JX5S/DP_aux_emulator/JLCPCB settings/1.png

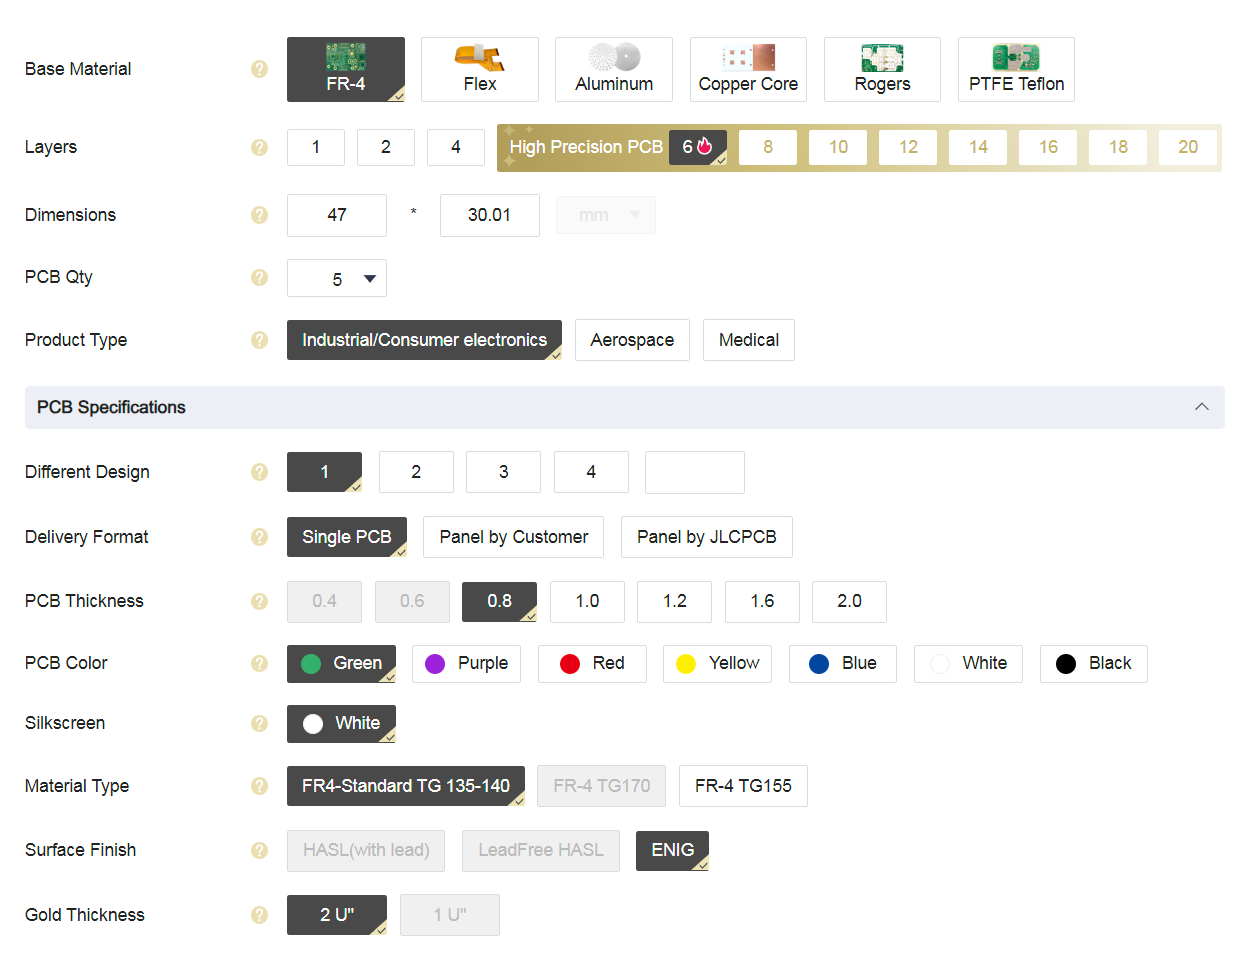
JLCPCB settings/1.png
