JX5S/DP_aux_emulator/JLCPCB settings/2.png

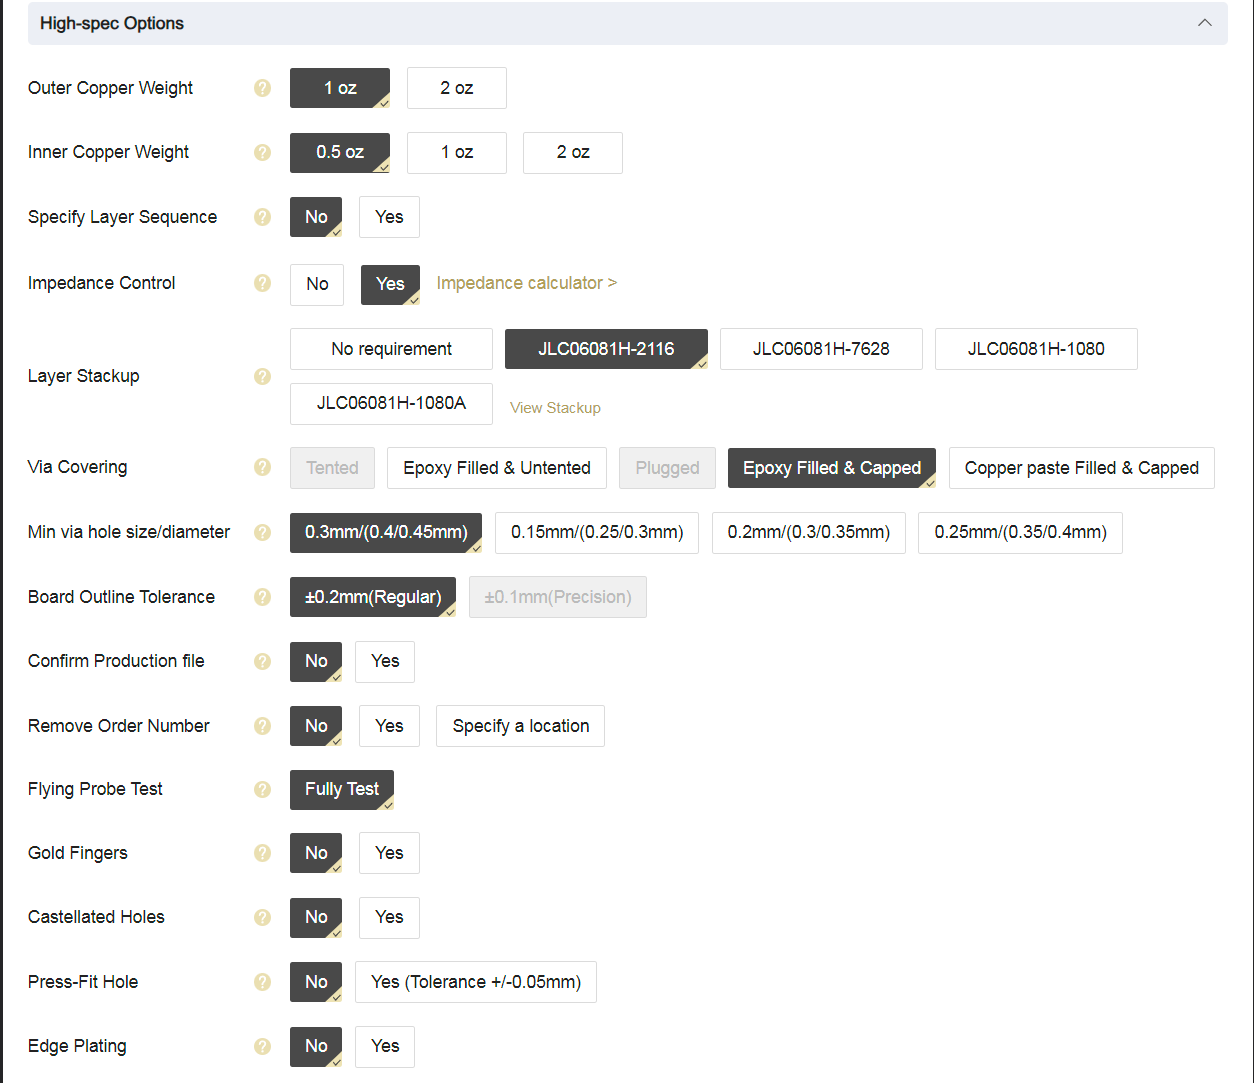
JLCPCB settings/2.png
