JX5S/DP_aux_emulator/JLCPCB settings/3.png

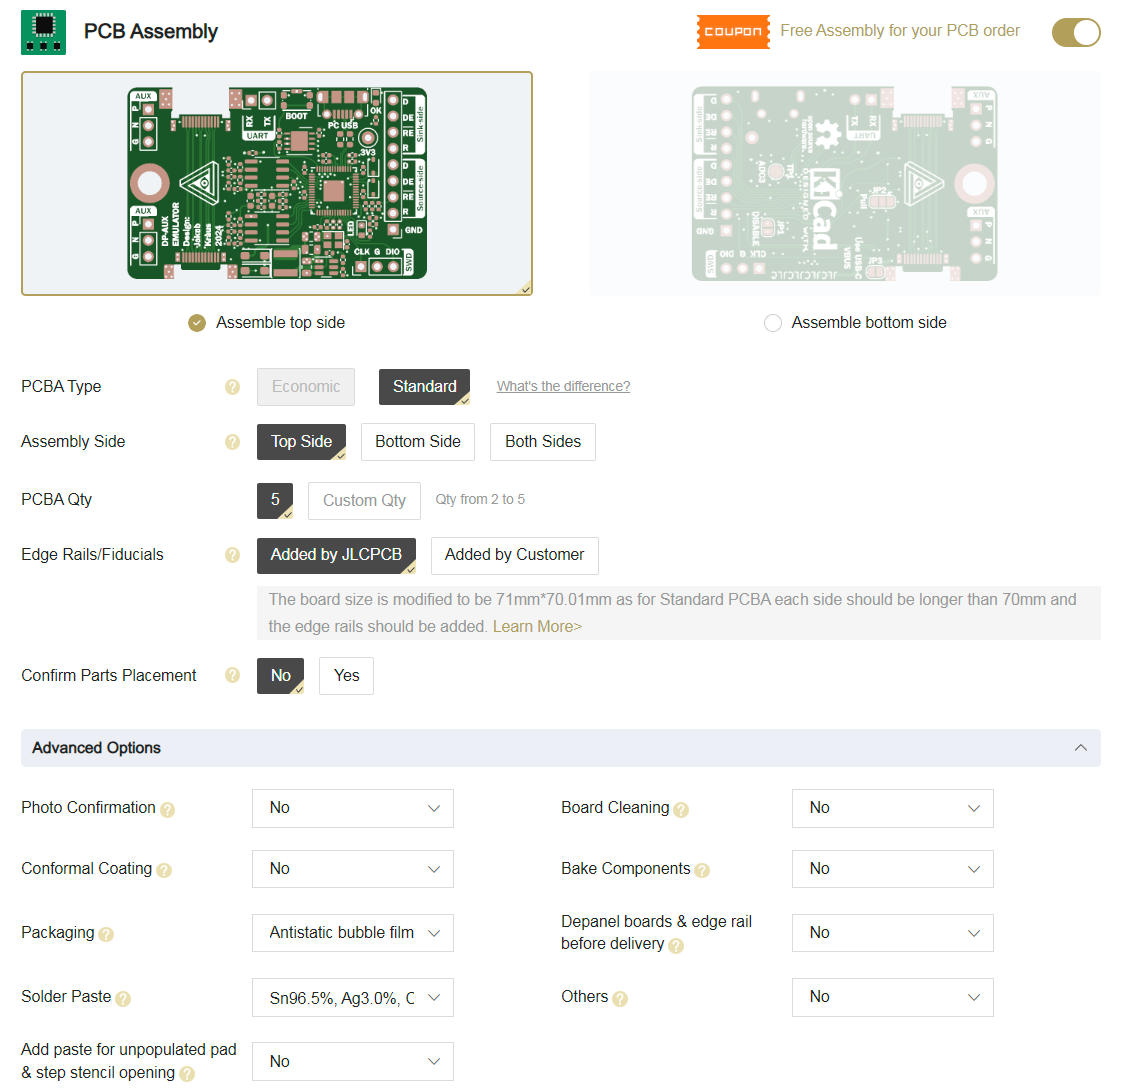
JLCPCB settings/3.png
